paulmandal/queensmatic/pictures/IMG_20170314_092558.jpg

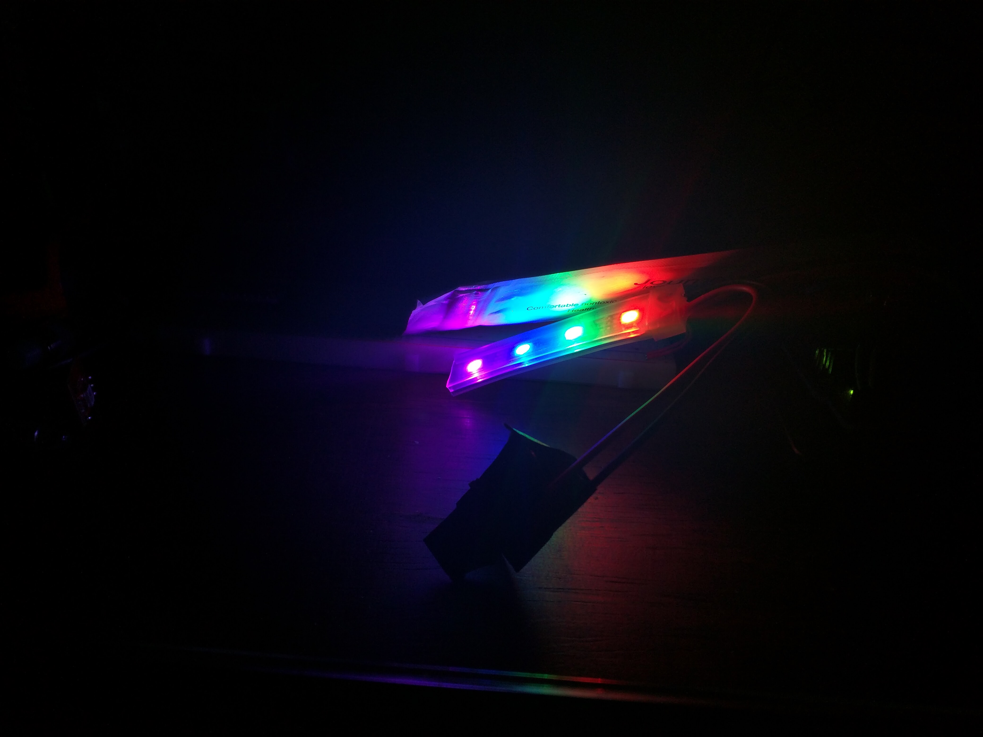
pictures/IMG_20170314_092558.jpg
