paulmandal/queensmatic/pictures/IMG_20170321_181850.jpg

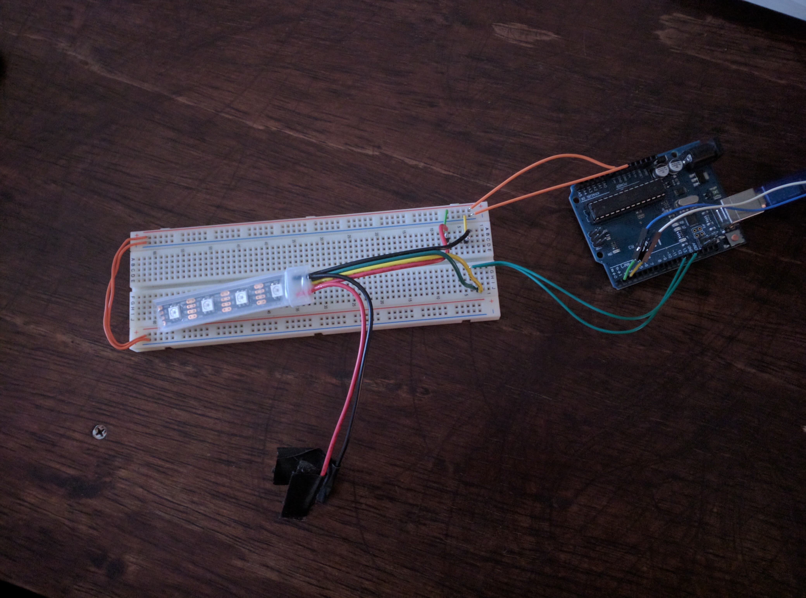
pictures/IMG_20170321_181850.jpg
