paulmandal/queensmatic/pictures/IMG_20170321_184949.jpg

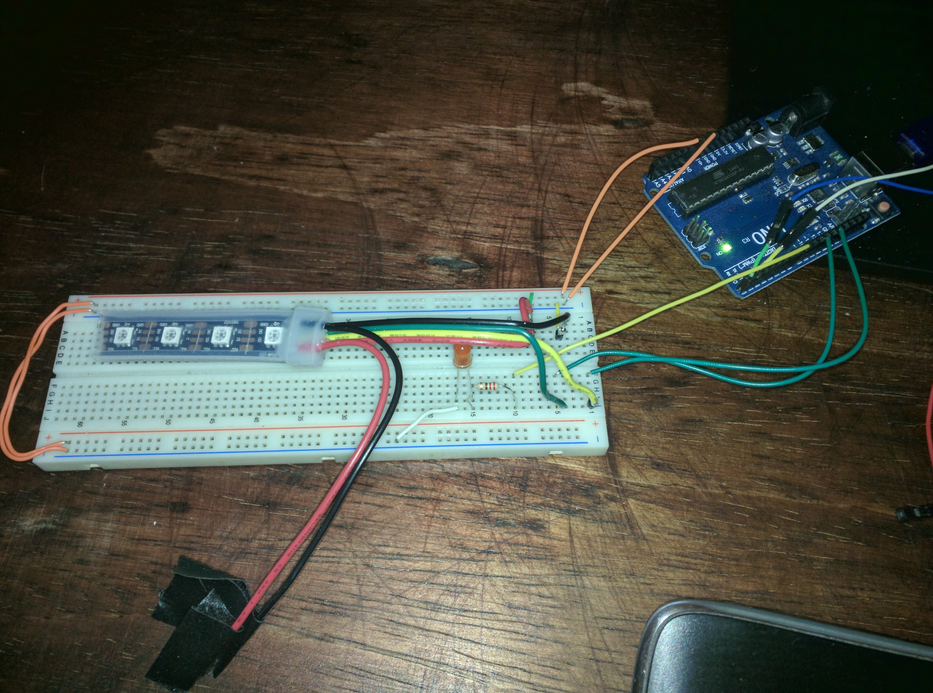
pictures/IMG_20170321_184949.jpg
