paulmandal/queensmatic/pictures/IMG_20170321_203158.jpg

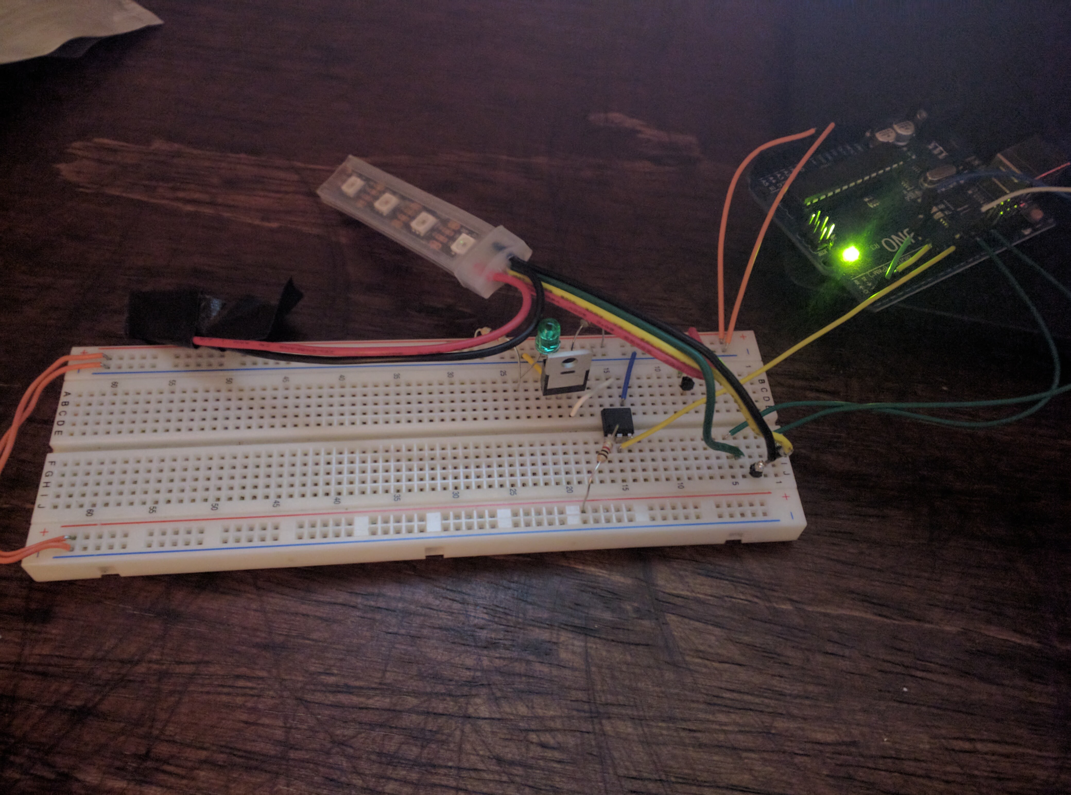
pictures/IMG_20170321_203158.jpg
