paulmandal/queensmatic/pictures/IMG_20170322_220235.jpg

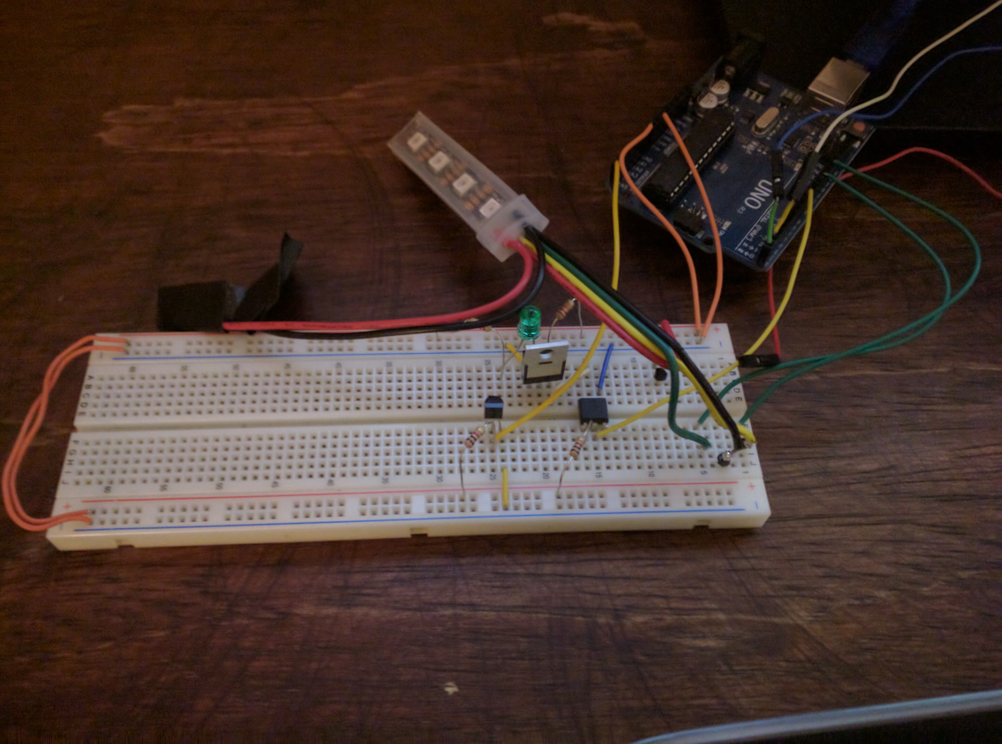
pictures/IMG_20170322_220235.jpg
