paulmandal/queensmatic/pictures/IMG_20170326_133836.jpg

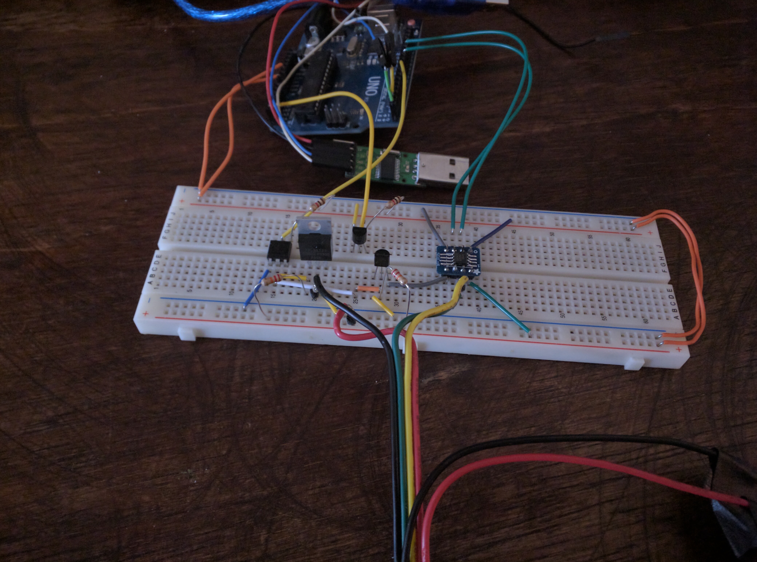
pictures/IMG_20170326_133836.jpg
