paulmandal/queensmatic/pictures/IMG_20170326_135756.jpg

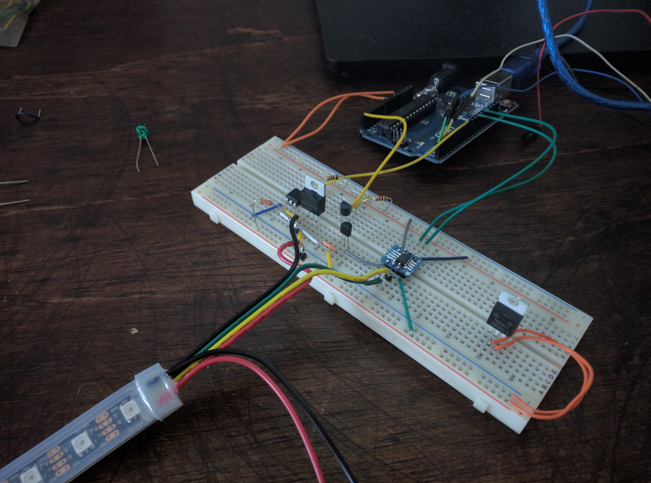
pictures/IMG_20170326_135756.jpg
