paulmandal/queensmatic/pictures/IMG_20170326_141339.jpg

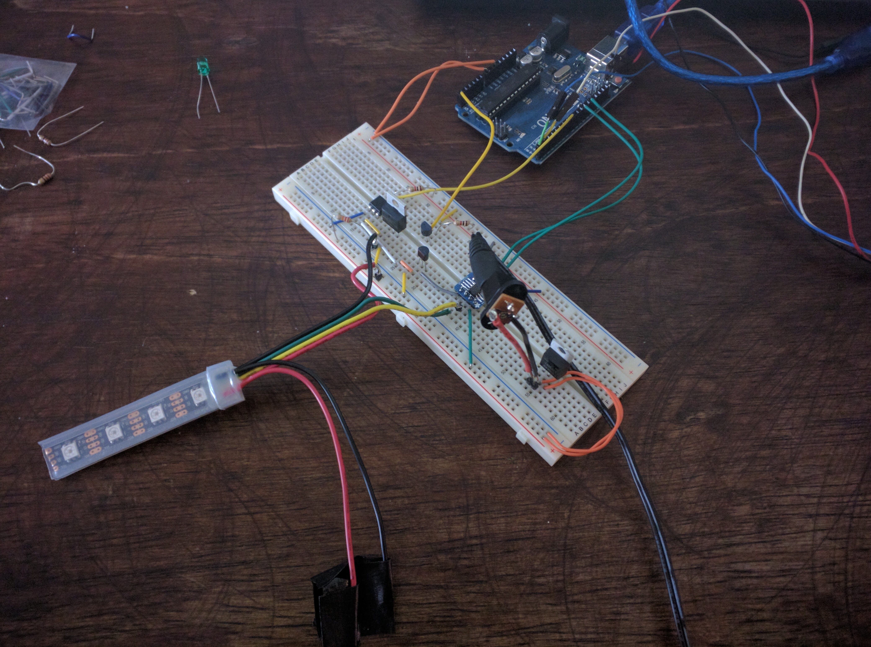
pictures/IMG_20170326_141339.jpg
