paulmandal/queensmatic/pictures/IMG_20170409_194634.jpg

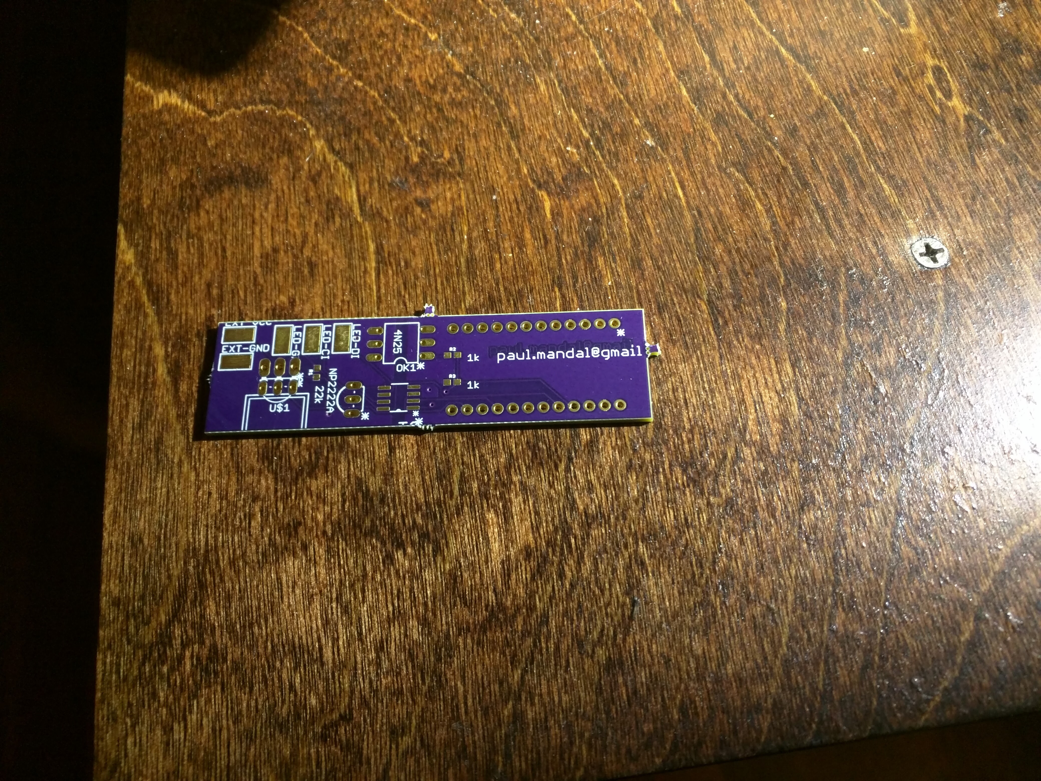
pictures/IMG_20170409_194634.jpg
