paulmandal/queensmatic/pictures/IMG_20170409_220346.jpg

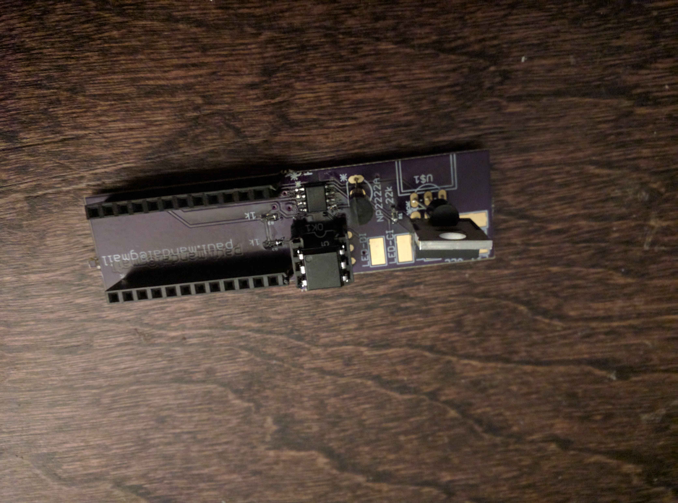
pictures/IMG_20170409_220346.jpg
