paulmandal/queensmatic/pictures/IMG_20170415_082219.jpg

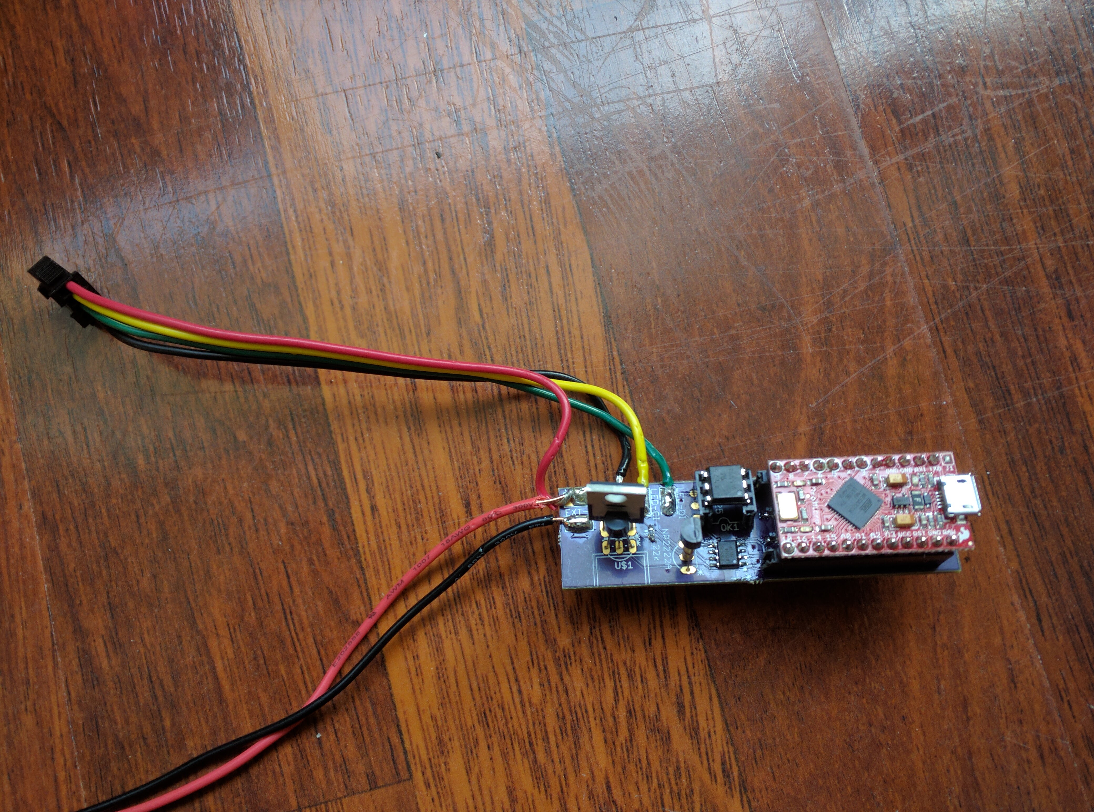
pictures/IMG_20170415_082219.jpg
