paulmandal/queensmatic/pictures/IMG_20170415_082541.jpg

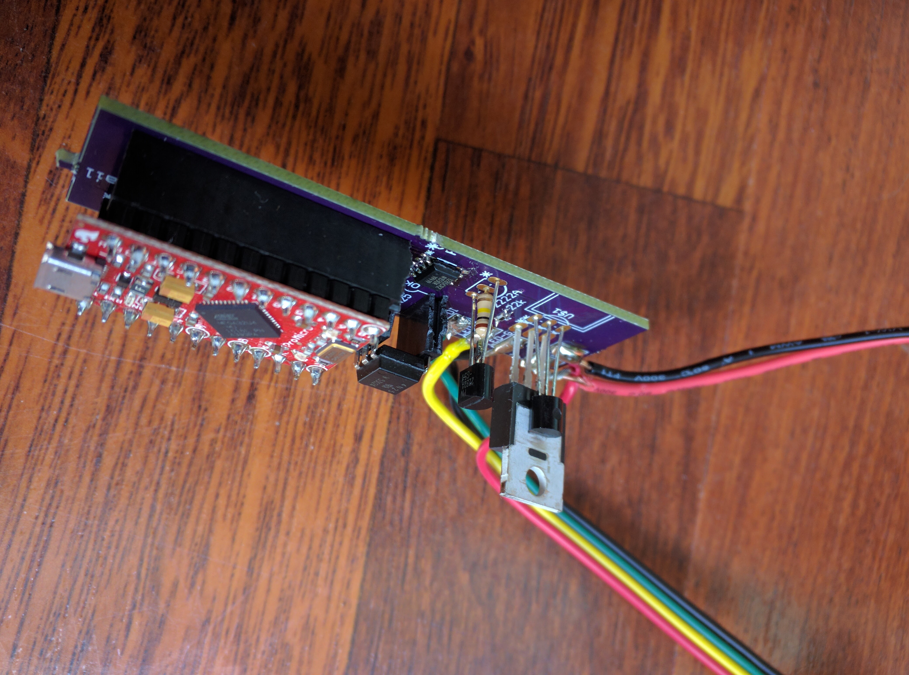
pictures/IMG_20170415_082541.jpg
