paulmandal/queensmatic/pictures/IMG_20170618_151922.jpg

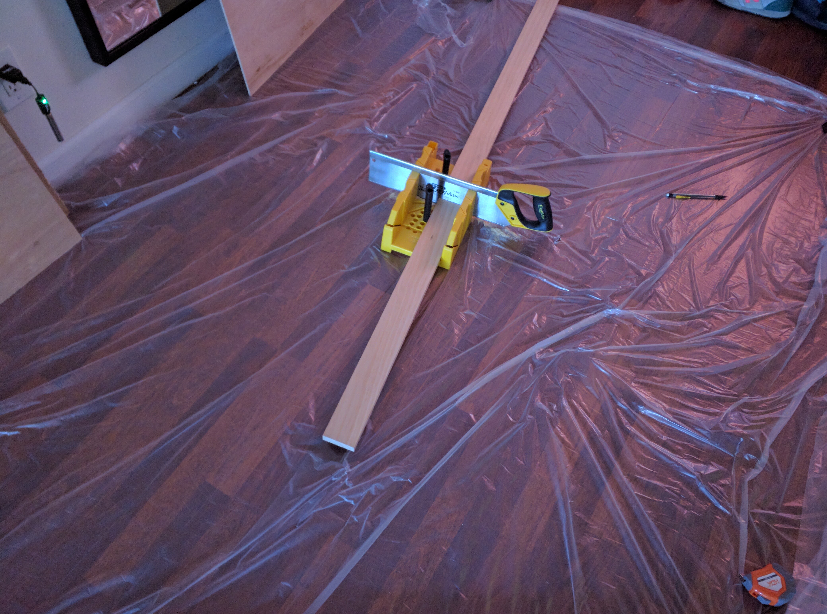
pictures/IMG_20170618_151922.jpg
