paulmandal/queensmatic/pictures/IMG_20170618_153749.jpg

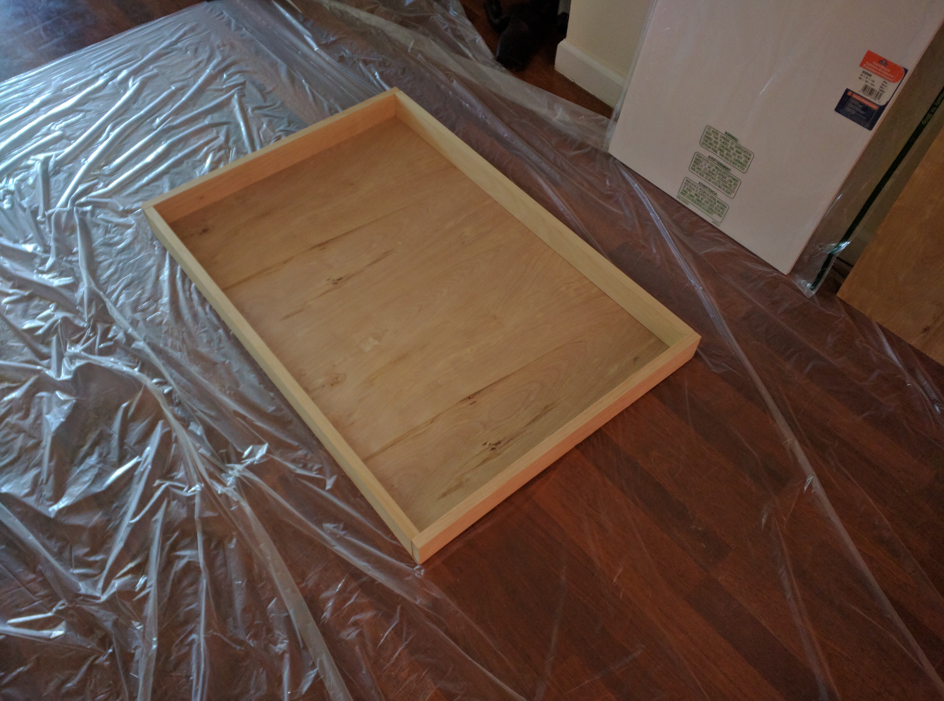
pictures/IMG_20170618_153749.jpg
