paulmandal/queensmatic/pictures/IMG_20170618_160940.jpg

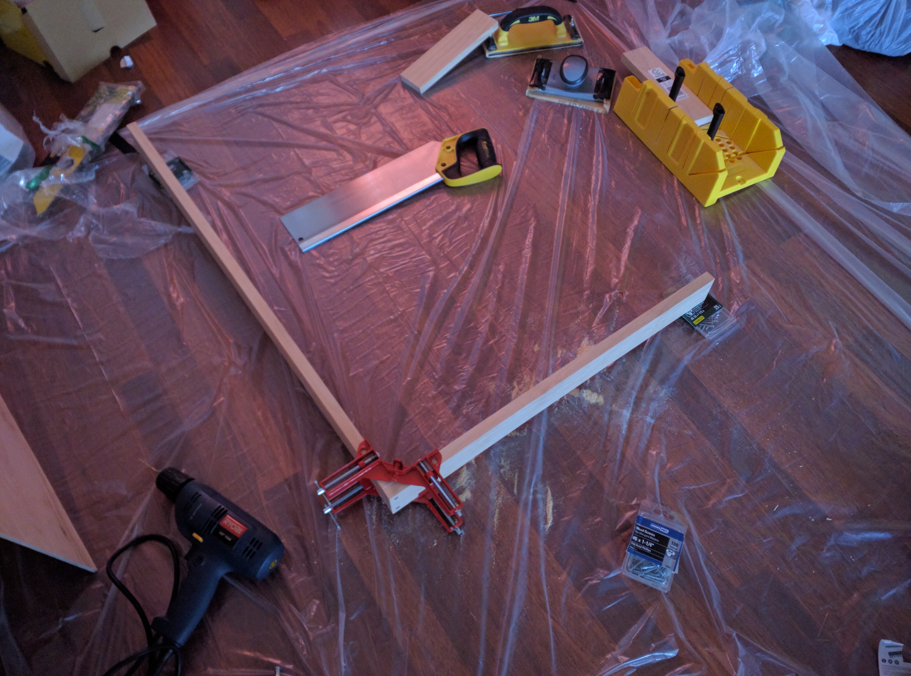
pictures/IMG_20170618_160940.jpg
