paulmandal/queensmatic/pictures/IMG_20170618_162314.jpg

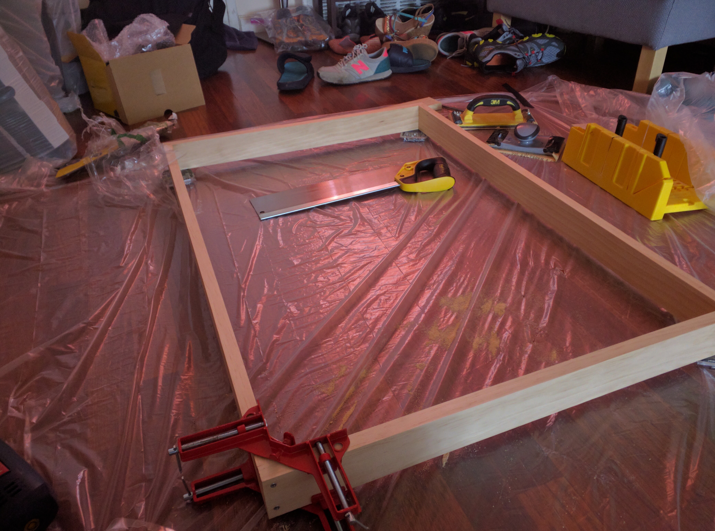
pictures/IMG_20170618_162314.jpg
