paulmandal/queensmatic/pictures/IMG_20170618_162947.jpg

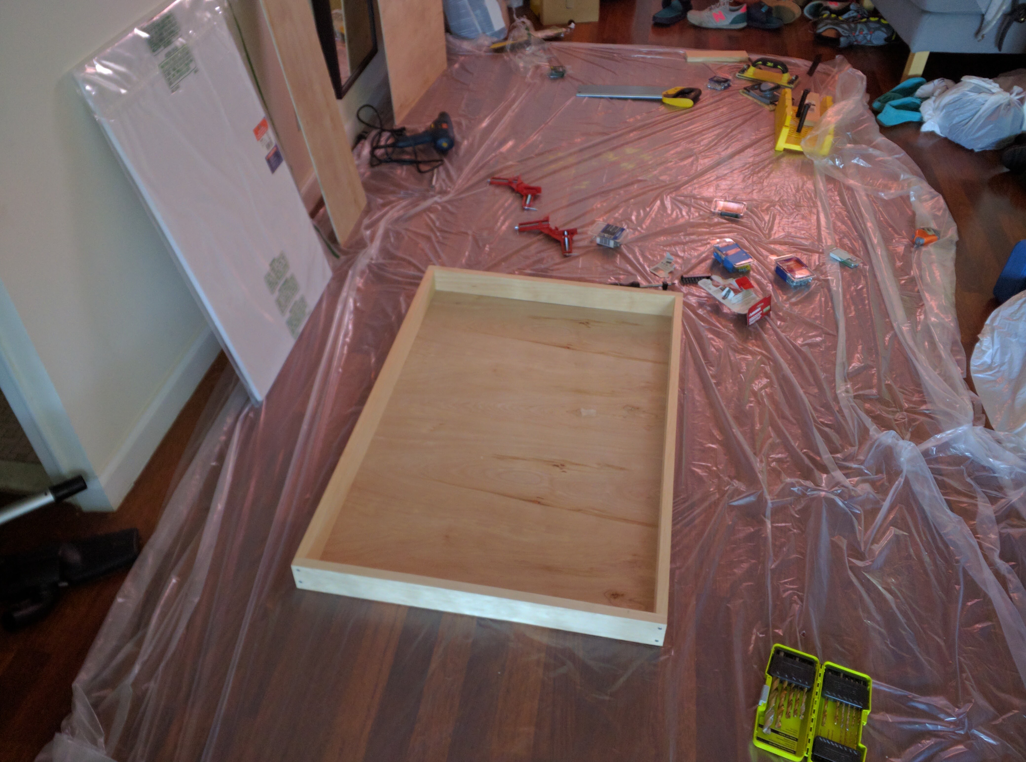
pictures/IMG_20170618_162947.jpg
