paulmandal/queensmatic/pictures/IMG_20170618_174707.jpg

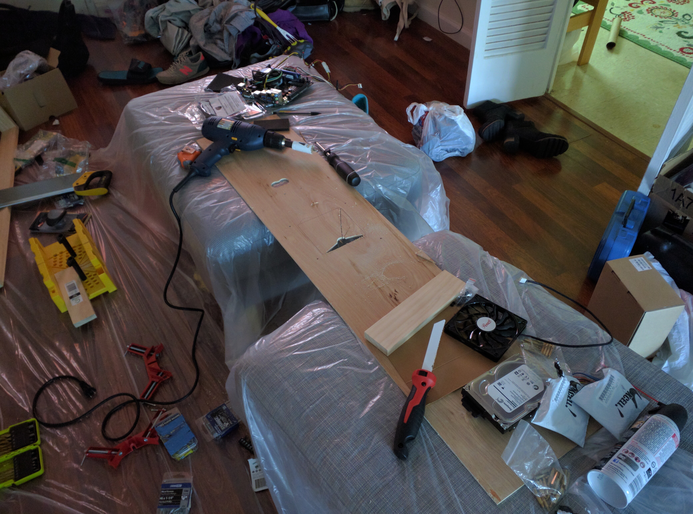
pictures/IMG_20170618_174707.jpg
