paulmandal/queensmatic/pictures/IMG_20170618_184759.jpg

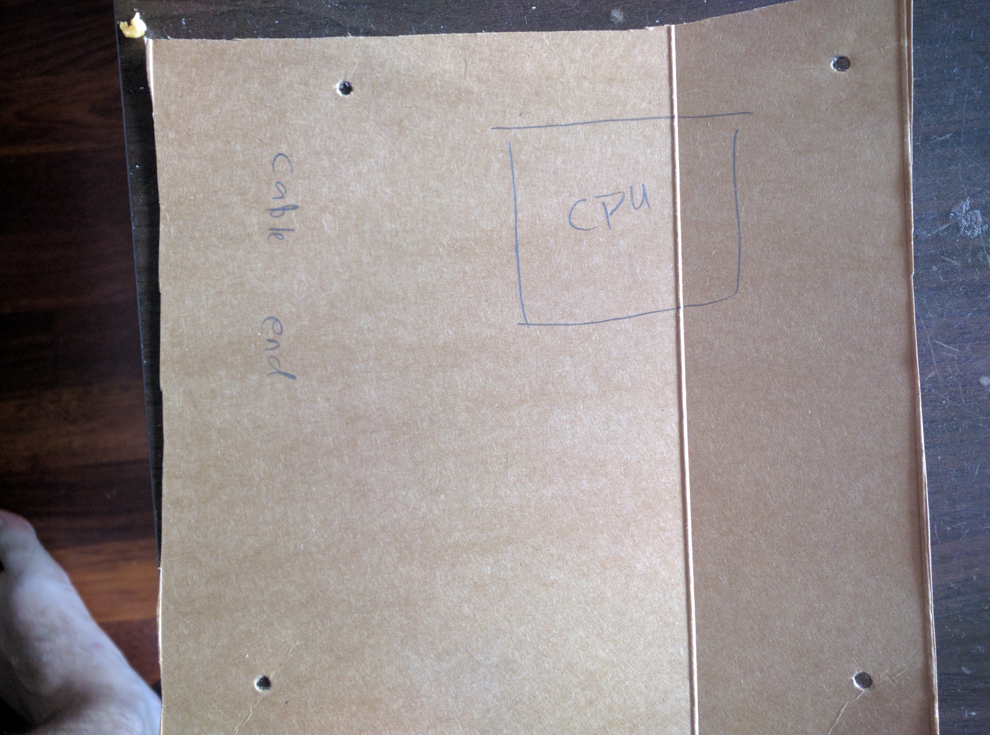
pictures/IMG_20170618_184759.jpg
