paulmandal/queensmatic/pictures/IMG_20170701_201217.jpg

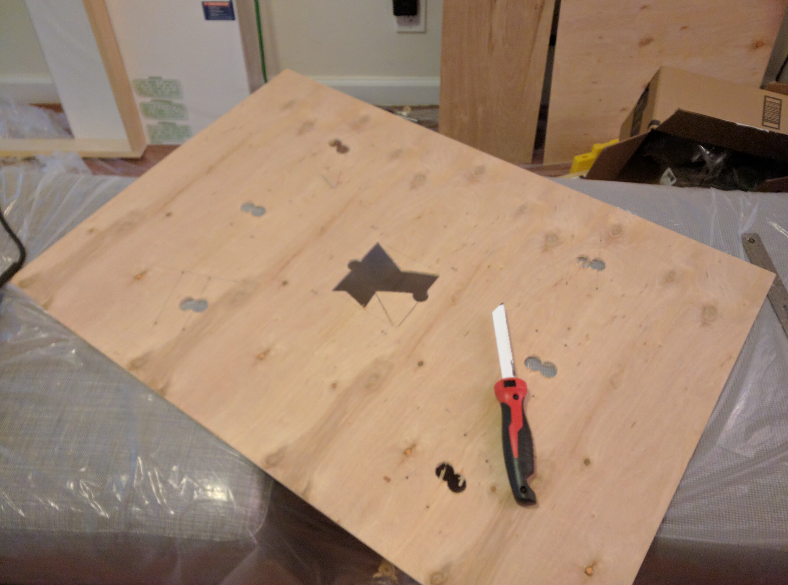
pictures/IMG_20170701_201217.jpg
