paulmandal/queensmatic/pictures/IMG_20170705_195913.jpg

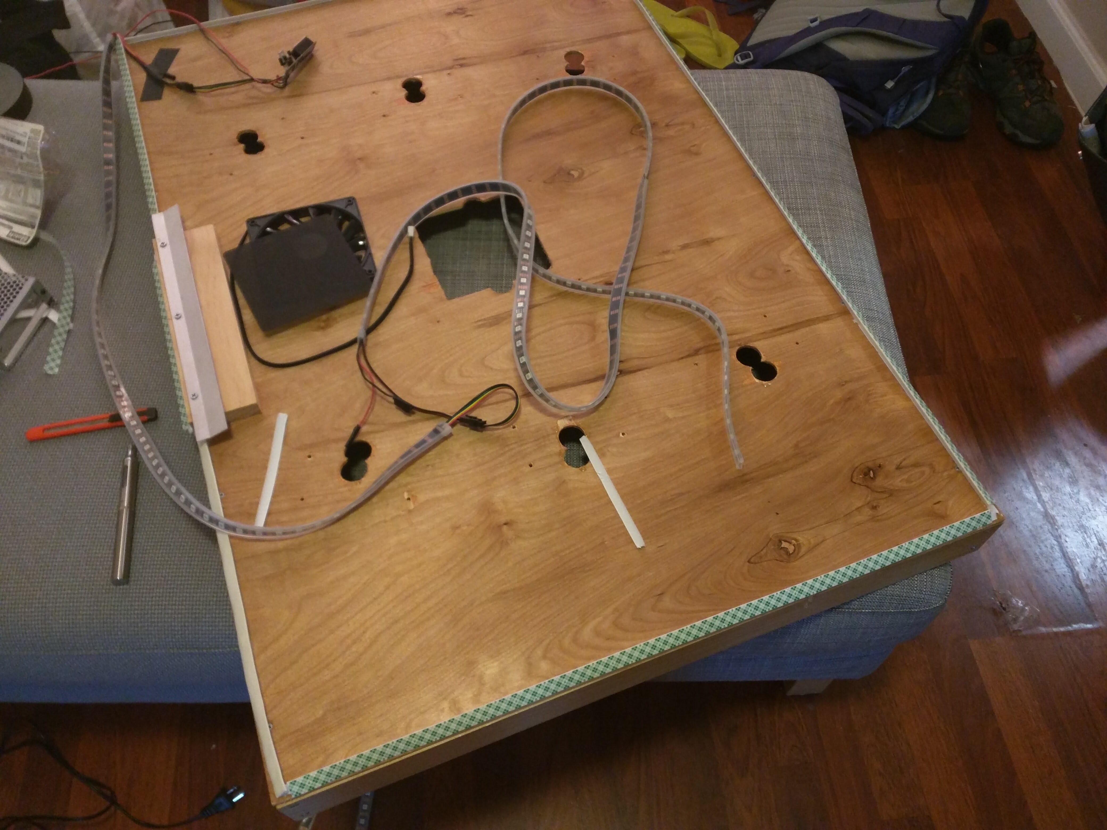
pictures/IMG_20170705_195913.jpg
