paulmandal/queensmatic/pictures/IMG_20170706_212039.jpg

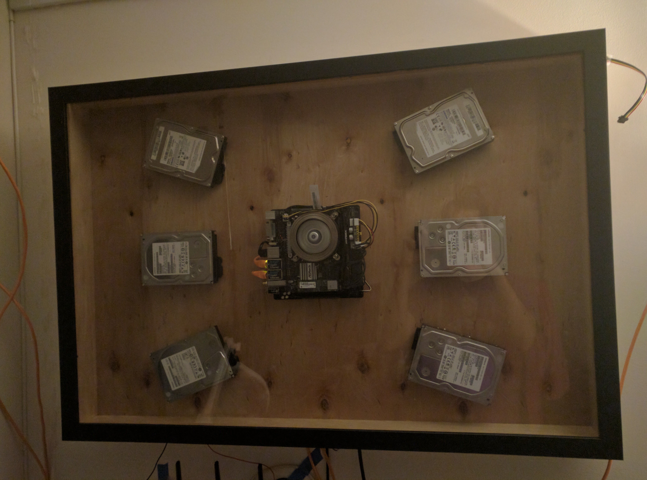
pictures/IMG_20170706_212039.jpg
