paulmandal/queensmatic/pictures/IMG_20170708_144542.jpg

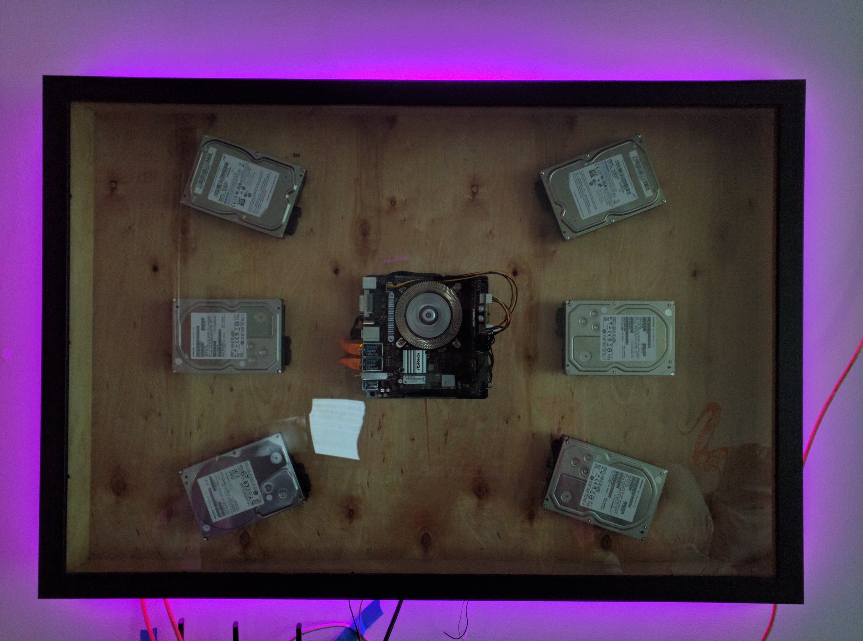
pictures/IMG_20170708_144542.jpg
