paulmandal/queensmatic/pictures/IMG_20170709_190251.jpg

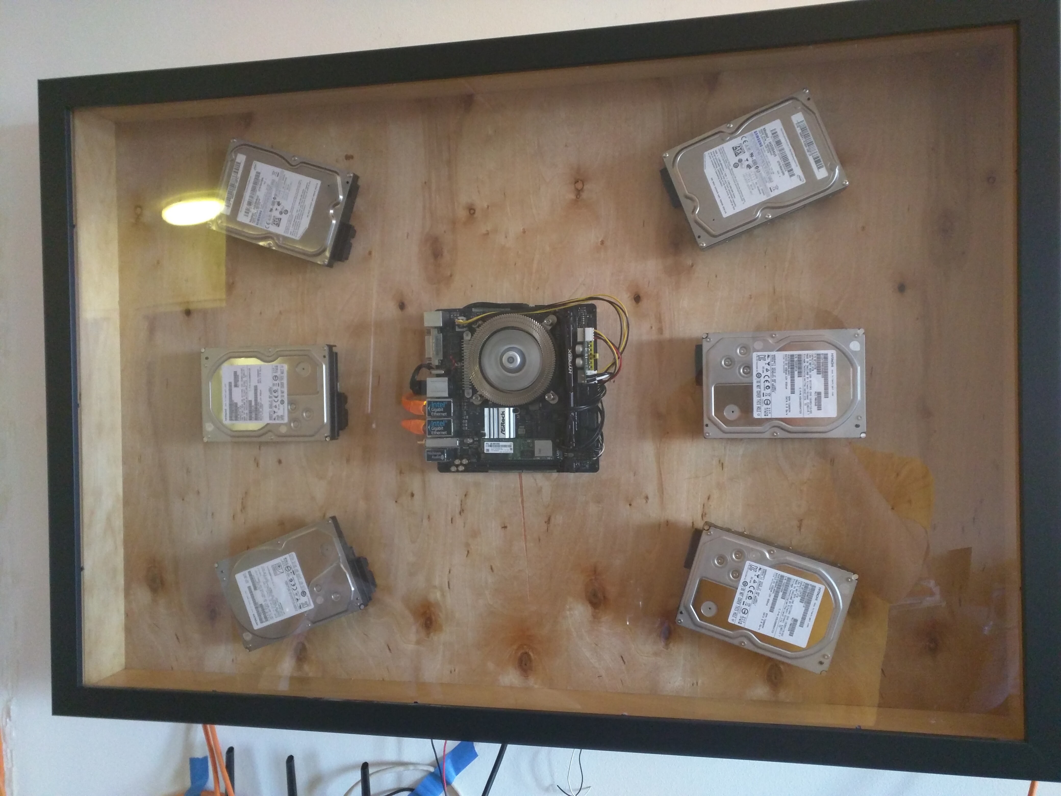
pictures/IMG_20170709_190251.jpg
