paulmandal/queensmatic/pictures/IMG_20170709_190303.jpg

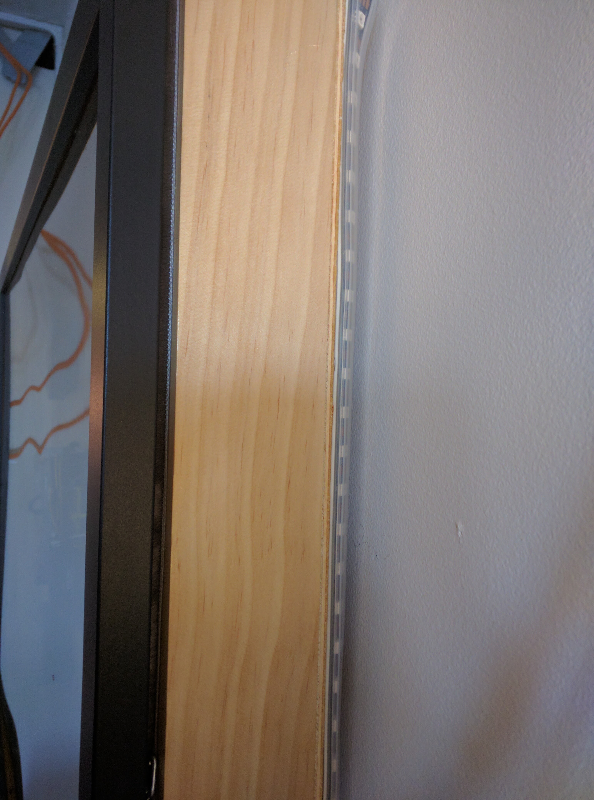
pictures/IMG_20170709_190303.jpg
