paulmandal/queensmatic/pictures/IMG_20170709_190308.jpg

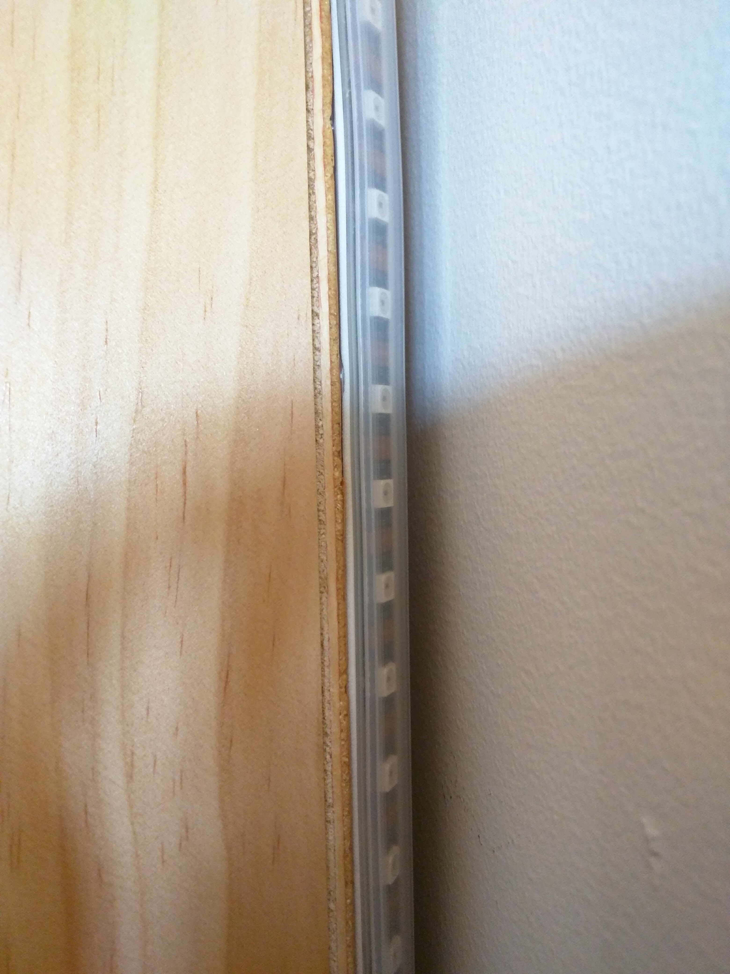
pictures/IMG_20170709_190308.jpg
