paulmandal/queensmatic/pictures/IMG_20170711_202655.jpg

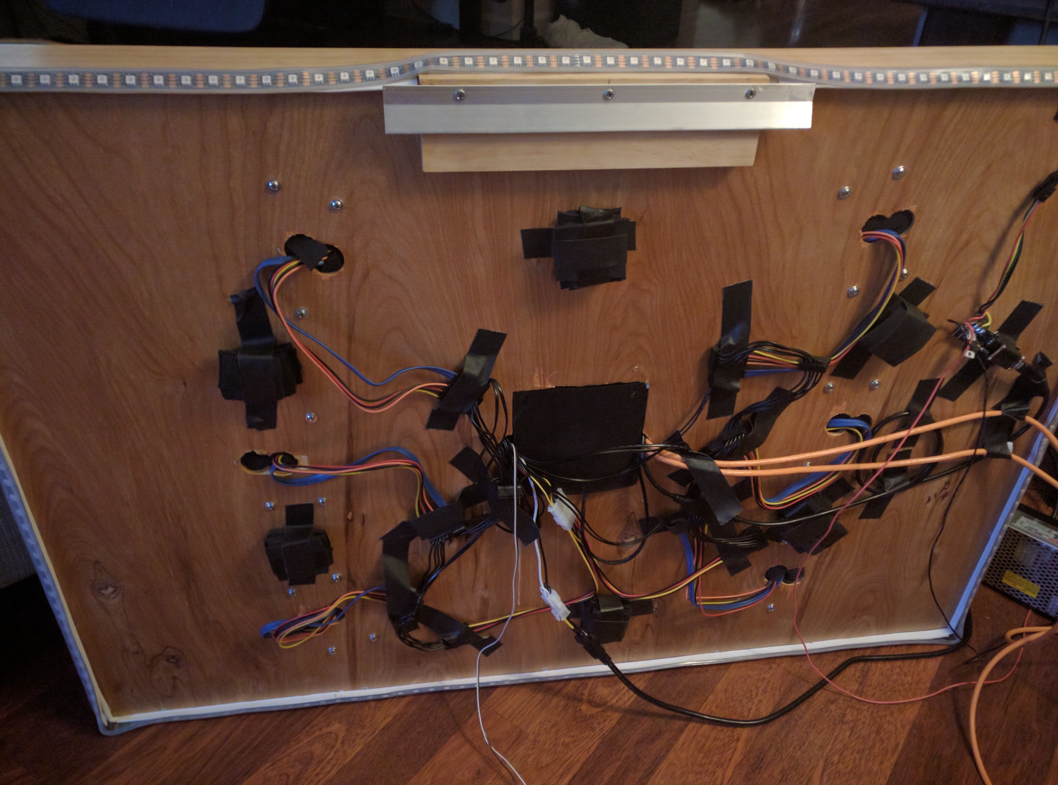
pictures/IMG_20170711_202655.jpg
