paulmandal/queensmatic/QueensmaticLEDController/app/src/main/java/com/paulmandal/queensmaticledcontroller/api/LedApi.java

package com.paulmandal.queensmaticledcontroller.api;

import android.content.Context;
import android.support.annotation.NonNull;

import com.android.volley.Cache;
import com.android.volley.Network;
import com.android.volley.Request;
import com.android.volley.RequestQueue;
import com.android.volley.Response;
import com.android.volley.VolleyError;
import com.android.volley.toolbox.BasicNetwork;
import com.android.volley.toolbox.DiskBasedCache;
import com.android.volley.toolbox.HurlStack;
import com.android.volley.toolbox.JsonObjectRequest;
import com.paulmandal.queensmaticledcontroller.data.Configuration;
import com.paulmandal.queensmaticledcontroller.data.Led;
import com.paulmandal.queensmaticledcontroller.data.SystemStatus;

import org.json.JSONObject;

/**
 * Handles communication with the API
 */
public class LedApi {

    /**
     * API Endpoints
     */
    private static final String CONFIGURATION_ENDPOINT = "/configuration";
    private static final String STATUS_ENDPOINT = "/status";
    private static final String LED_UPDATE_ENDPOINT = "/leds";

    /**
     * Callback for fetching a Configuration
     */
    public interface FetchConfigurationListener {
        void onConfigurationFetched(@NonNull Configuration configuration);

        void onConfigurationFetchError();
    }

    /**
     * Callback for fetching the system status
     */
    public interface FetchSystemStatusListener {
        void onSystemStatusFetched(@NonNull SystemStatus systemStatus);

        void onSystemStatusFetchError();
    }

    /**
     * Callback for storing a Configuration
     */
    public interface StoreConfigurationListener {
        void onConfigurationStored();

        void onConfigurationStoreError();
    }

    /**
     * Volley Request Queue
     */
    private final RequestQueue mRequestQueue;

    /**
     * Hostname for API requests
     */
    private String mHostname;

    public LedApi(RequestQueue requestQueue, String hostname) {
        mRequestQueue = requestQueue;
        mHostname = hostname;
        mRequestQueue.start();
    }

    /**
     * Factory method for creating LedApi instances
     */
    public static LedApi ledApiFactory(Context context, String hostname) {
        Cache cache = new DiskBasedCache(context.getCacheDir(), 1024);
        Network network = new BasicNetwork(new HurlStack());
        return new LedApi(new RequestQueue(cache, network), hostname);
    }

    /**
     * Set the hostname this LedApi instance will send commands to
     *
     * @param hostname The hostname this LedApi instance will send commands to
     */
    public void setHostname(String hostname) {
        mHostname = hostname;
    }

    /**
     * Fetches the configuration from the API
     *
     * @param listener Callback after async fetch
     */
    public void fetchConfiguration(final FetchConfigurationListener listener) {
        JsonObjectRequest request = new JsonObjectRequest
                (Request.Method.GET, mHostname + CONFIGURATION_ENDPOINT, null, new Response.Listener<JSONObject>() {
                    FetchConfigurationListener mListener = listener;

                    @Override
                    public void onResponse(JSONObject response) {
                        Configuration configuration = ApiTranslator.configurationFromJson(response);
                        if (configuration != null) {
                            mListener.onConfigurationFetched(configuration);
                        } else {
                            mListener.onConfigurationFetchError();
                        }
                    }
                }, new Response.ErrorListener() {
                    FetchConfigurationListener mListener = listener;

                    @Override
                    public void onErrorResponse(VolleyError error) {
                        error.printStackTrace();
                        mListener.onConfigurationFetchError();
                    }
                });
        addRequest(request);
    }

    /**
     * Stores a Configuration using the API
     *
     * @param listener      Callback for async store operation
     * @param configuration
     */
    public void sendConfiguration(final StoreConfigurationListener listener, Configuration configuration) {
        JSONObject json = ApiTranslator.jsonObjectFromConfiguration(configuration);
        if (json != null) {
            JsonObjectRequest request = new JsonObjectRequest
                    (Request.Method.PUT, mHostname + CONFIGURATION_ENDPOINT, json, new Response.Listener<JSONObject>() {
                        StoreConfigurationListener mListener = listener;

                        @Override
                        public void onResponse(JSONObject response) {
                            mListener.onConfigurationStored();
                        }
                    }, new Response.ErrorListener() {
                        StoreConfigurationListener mListener = listener;

                        @Override
                        public void onErrorResponse(VolleyError error) {
                            error.printStackTrace();
                            mListener.onConfigurationStoreError();
                        }
                    });
            addRequest(request);
        } else {
            listener.onConfigurationStoreError();
        }
    }

    /**
     * Fetches the system status from the API
     *
     * @param listener Callback after async fetch
     */
    public void fetchSystemStatus(final FetchSystemStatusListener listener) {
        JsonObjectRequest request = new JsonObjectRequest
                (Request.Method.GET, mHostname + STATUS_ENDPOINT, null, new Response.Listener<JSONObject>() {
                    FetchSystemStatusListener mListener = listener;

                    @Override
                    public void onResponse(JSONObject response) {
                        SystemStatus systemStatus = ApiTranslator.systemStatusFromJson(response);
                        if (systemStatus != null) {
                            mListener.onSystemStatusFetched(systemStatus);
                        } else {
                            mListener.onSystemStatusFetchError();
                        }
                    }
                }, new Response.ErrorListener() {
                    FetchSystemStatusListener mListener = listener;

                    @Override
                    public void onErrorResponse(VolleyError error) {
                        error.printStackTrace();
                        mListener.onSystemStatusFetchError();
                    }
                });
        addRequest(request);
    }

    /**
     * Sends a Power State update to the LED API
     *
     * @param powerState New power state for the LED strips
     */
    public void sendPowerUpdate(boolean powerState) {
        JSONObject json = ApiTranslator.jsonObjectFromSystemStatus(new SystemStatus(powerState, 0.0f));
        if (json != null) {
            JsonObjectRequest request = new JsonObjectRequest(Request.Method.PUT, mHostname + STATUS_ENDPOINT, json, new Response.Listener<JSONObject>() {
                @Override
                public void onResponse(JSONObject response) { /* Do nothing */ }
            }, new Response.ErrorListener() {
                @Override
                public void onErrorResponse(VolleyError error) {
                    error.printStackTrace();
                }
            });
            addRequest(request);
        }
    }

    /**
     * Sends an LED Update to the API - these are sent blind (no callback) because the user
     * should be able to visually confirm that the updates are happening, error reporting/handling
     * of some kind would be a nice addition, though.
     *
     * @param led The LED to update
     */
    public void sendLedUpdate(Led led) {
        JSONObject json = ApiTranslator.jsonObjectFromLed(led);
        if (json != null) {
            JsonObjectRequest request = new JsonObjectRequest
                    (Request.Method.PUT, mHostname + LED_UPDATE_ENDPOINT, json, new Response.Listener<JSONObject>() {
                        @Override
                        public void onResponse(JSONObject response) { /* Do nothing */ }
                    }, new Response.ErrorListener() {
                        @Override
                        public void onErrorResponse(VolleyError error) {
                            error.printStackTrace();
                        }
                    });
            addRequest(request);
        }
    }

    /**
     * Disables caching and sends the request to the queue
     *
     * @param request JSONObject Volley request
     */
    private void addRequest(Request request) {
        request.setShouldCache(false);
        mRequestQueue.add(request);
    }

}
