paulmandal/queensmatic/led-controller-uservice/constants.py

#!venv/bin/python

#
# Various Constants
#

DATABASE_FILE = 'uservice-db.sqlite'
CONFIG_TABLE_NAME = 'led_configuration'
LED_UPDATE_FIELDS = ['ledNumber', 'red', 'green', 'blue', 'brightness']
USB_SERIAL = '/dev/ttyACM0'
